IvanLi-CN/pd-sink-stm32-rs/src/font.rs

pub static DOT_MATRIX_XL_NUM: &[&[u8; 200]; 10] = &[
    &[
        0x00, 0x00, 0x00, 0x00, 0x00, 0xE3, 0x8E, 0x00, 0x01, 0xF7, 0xDF, 0x00, 0x01, 0xF7, 0xDF,
        0x00, 0x01, 0xF7, 0xDF, 0x00, 0x00, 0xE3, 0x8E, 0x00, 0x00, 0x00, 0x00, 0x00, 0x00, 0x00,
        0x00, 0x00, 0x38, 0x00, 0x00, 0x38, 0x7C, 0x00, 0x00, 0x7C, 0x7C, 0x00, 0x00, 0x7C, 0x7C,
        0x00, 0x00, 0x7C, 0x38, 0x00, 0x00, 0x38, 0x00, 0x00, 0x00, 0x00, 0x00, 0x00, 0x00, 0x00,
        0x38, 0x00, 0x00, 0x38, 0x7C, 0x00, 0x00, 0x7C, 0x7C, 0x00, 0x00, 0x7C, 0x7C, 0x00, 0x00,
        0x7C, 0x38, 0x00, 0x00, 0x38, 0x00, 0x00, 0x00, 0x00, 0x00, 0x00, 0x00, 0x00, 0x38, 0x00,
        0x00, 0x38, 0x7C, 0x00, 0x00, 0x7C, 0x7C, 0x00, 0x00, 0x7C, 0x7C, 0x00, 0x00, 0x7C, 0x38,
        0x00, 0x00, 0x38, 0x00, 0x00, 0x00, 0x00, 0x00, 0x00, 0x00, 0x00, 0x38, 0x00, 0x00, 0x38,
        0x7C, 0x00, 0x00, 0x7C, 0x7C, 0x00, 0x00, 0x7C, 0x7C, 0x00, 0x00, 0x7C, 0x38, 0x00, 0x00,
        0x38, 0x00, 0x00, 0x00, 0x00, 0x00, 0x00, 0x00, 0x00, 0x38, 0x00, 0x00, 0x38, 0x7C, 0x00,
        0x00, 0x7C, 0x7C, 0x00, 0x00, 0x7C, 0x7C, 0x00, 0x00, 0x7C, 0x38, 0x00, 0x00, 0x38, 0x00,
        0x00, 0x00, 0x00, 0x00, 0x00, 0x00, 0x00, 0x00, 0xE3, 0x8E, 0x00, 0x01, 0xF7, 0xDF, 0x00,
        0x01, 0xF7, 0xDF, 0x00, 0x01, 0xF7, 0xDF, 0x00, 0x00, 0xE3, 0x8E, 0x00, 0x00, 0x00, 0x00,
        0x00, 0x00, 0x00, 0x00, 0x00,
    ], // 0
    &[
        0x00, 0x00, 0x00, 0x00, 0x00, 0x03, 0x80, 0x00, 0x00, 0x07, 0xC0, 0x00, 0x00, 0x07, 0xC0,
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
        defmt::error!("unknown char: {}", c);
        0
    })
}

pub fn get_indexes_by_str<'a>(index: &[char], s: &str, buff: &'a mut [usize]) -> &'a [usize] {
    for (i, c) in s.chars().enumerate() {
        buff[i] = get_index_by_char(index, c);
    }

    buff
}
